PotatoSlop/Nob/SLDPRT/v3baseCollar.SLDPRT

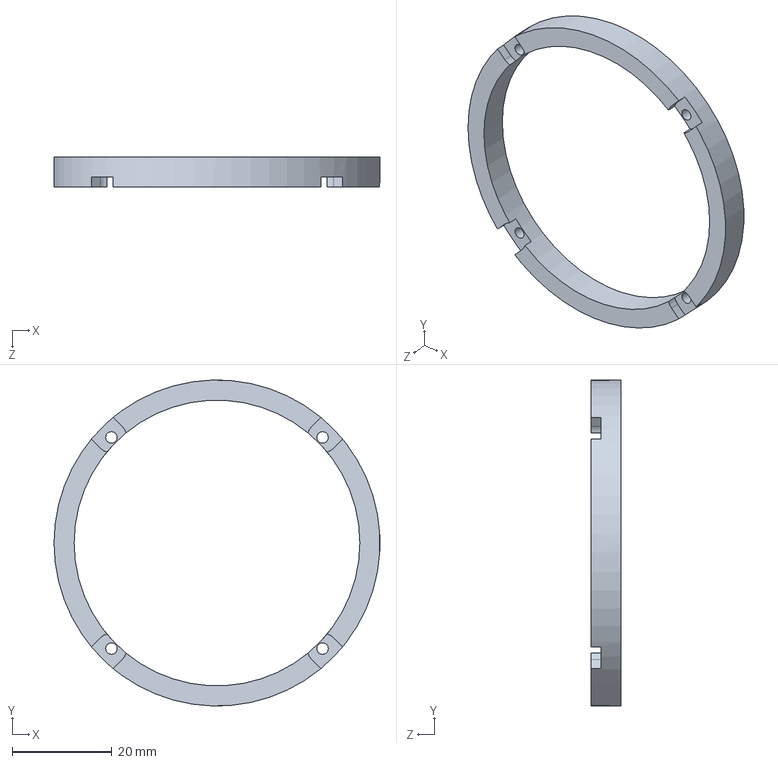
[picture p20: CAD file, 2026-09-04]
SLDPRT/v3baseCollar.SLDPRT
65.5 x 65.5 x 6.00 mm
