PotatoSlop/Nob/SLDPRT/Reference 3D Models/focus-dial-main/focus-dial-main/cad/STLs/Bezel.stl

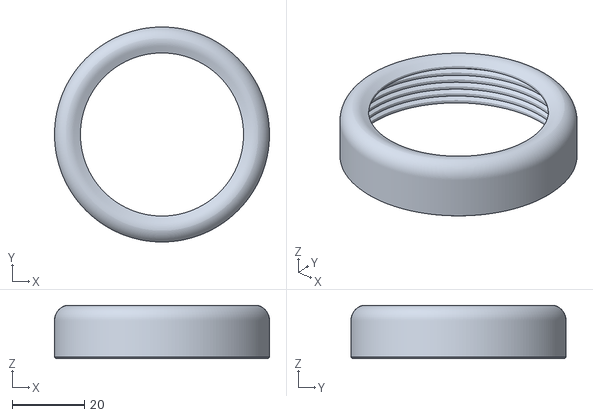
[picture p21: CAD file, 2025-09-17]
SLDPRT/Reference 3D Models/focus-dial-main/focus-dial-main/cad/STLs/Bezel.stl
59.6 x 59.6 x 14.7
