PotatoSlop/Nob/SLDPRT/shell_top_inner_2.SLDPRT

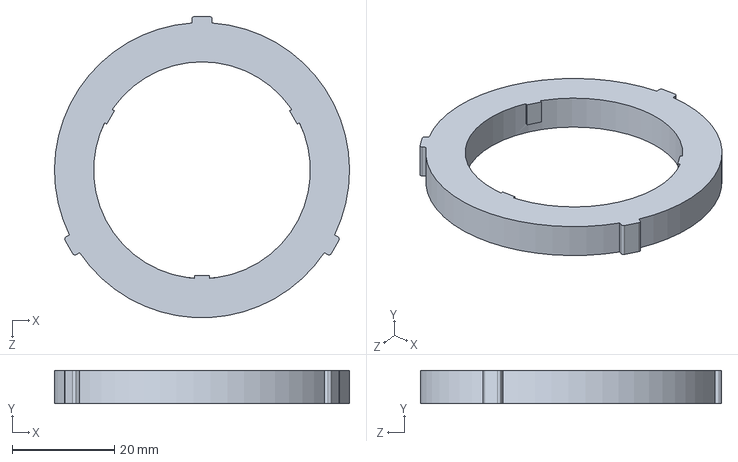
[picture p22: CAD file, 2026-09-04]
SLDPRT/shell_top_inner_2.SLDPRT
57.6 x 6.50 x 58.8 mm
