PotatoSlop/Nob/SLDPRT/Reference 3D Models/focus-dial-main/focus-dial-main/cad/STLs/Face.stl

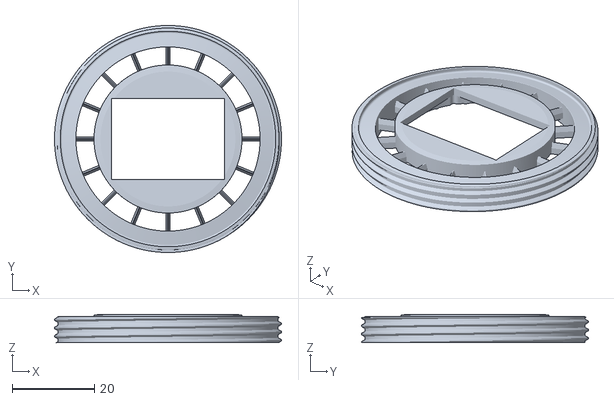
[picture p23: CAD file, 2025-09-17]
SLDPRT/Reference 3D Models/focus-dial-main/focus-dial-main/cad/STLs/Face.stl
55.2 x 55.2 x 6.90
