PotatoSlop/Nob/SLDPRT/Reference 3D Models/focus-dial-main/focus-dial-main/cad/STLs/Button Cap.stl

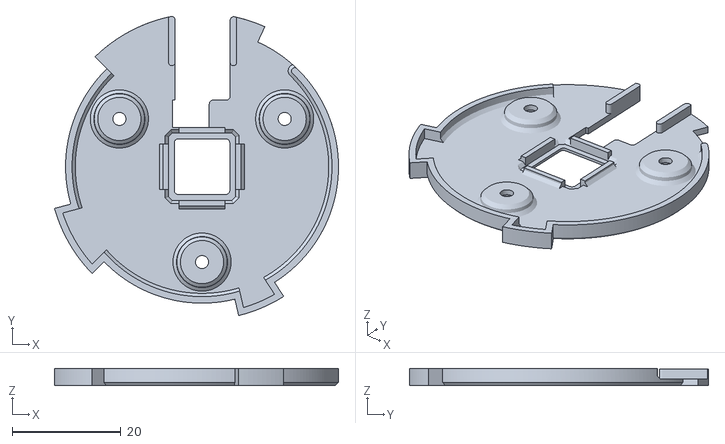
[picture p24: CAD file, 2025-09-17]
SLDPRT/Reference 3D Models/focus-dial-main/focus-dial-main/cad/STLs/Button Cap.stl
52.2 x 55.0 x 3.20
