PotatoSlop/Nob/SLDPRT/v3baseShellTopHalf.SLDPRT

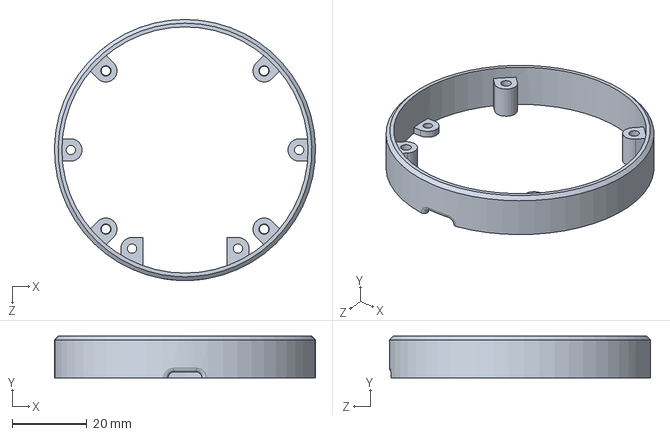
[picture p25: CAD file, 2026-09-04]
SLDPRT/v3baseShellTopHalf.SLDPRT
70.0 x 11.2 x 70.0 mm
