PotatoSlop/Nob/SLDPRT/Reference 3D Models/focus-dial-main/focus-dial-main/cad/STLs/Screen Backing.stl

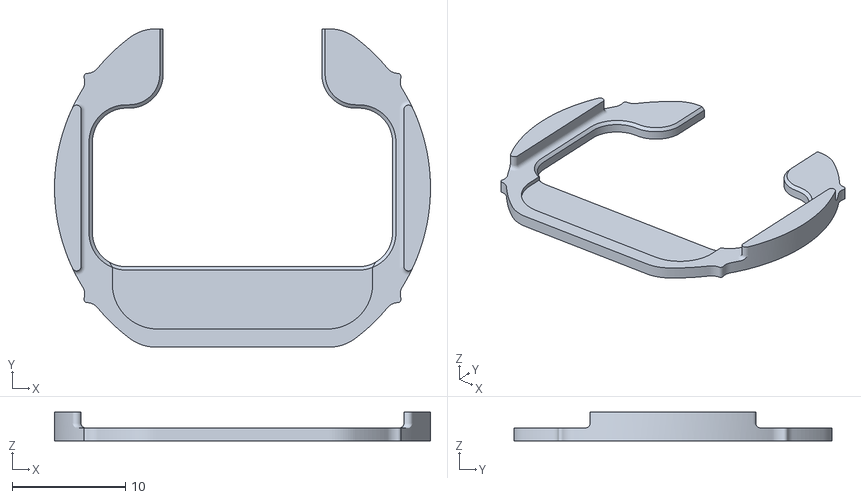
[picture p26: CAD file, 2025-09-17]
SLDPRT/Reference 3D Models/focus-dial-main/focus-dial-main/cad/STLs/Screen Backing.stl
33.2 x 28.1 x 2.55
