PotatoSlop/Nob/SLDPRT/Reference 3D Models/focus-dial-main/focus-dial-main/cad/STLs/Central Shaft.stl

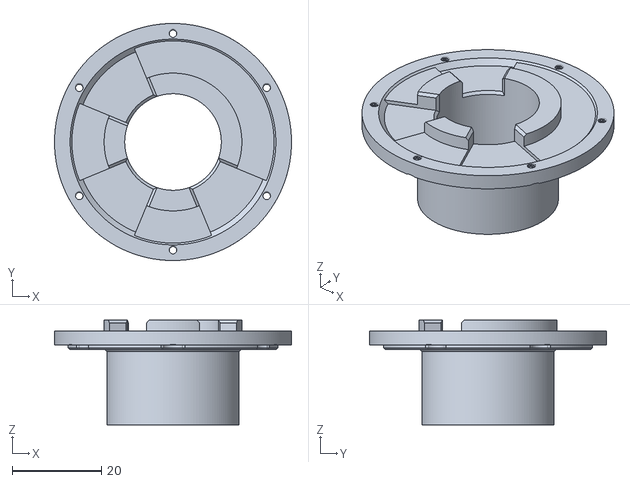
[picture p27: CAD file, 2025-09-17]
SLDPRT/Reference 3D Models/focus-dial-main/focus-dial-main/cad/STLs/Central Shaft.stl
53.0 x 53.0 x 23.4
