PotatoSlop/Nob/SLDPRT/Full.SLDASM

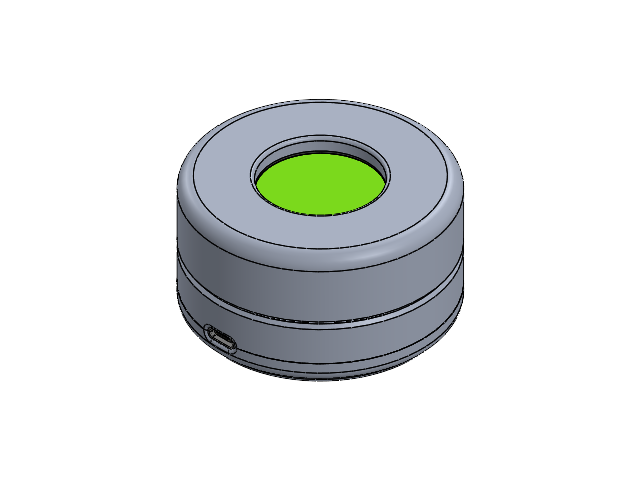
[picture p29: CAD file, 2026-09-04]
SLDPRT/Full.SLDASM
baseShellBotHalf
baseShellTopHalf
External Case.step
Steel Plate.step
Push Button.step
Component4.step x 4
EC50A0920404.step
shell_top_inner_2
inner_tube
Shell_top2_1
LCD 1.28 Inch GC9A01.stp
BOSS-EXTRUDE14_8_.step
BOSS-EXTRUDE7_4_.step
BOSS-EXTRUDE7_3_.step
BOSS-EXTRUDE14_4_.step
BOSS-EXTRUDE14_2_.step
BOSS-EXTRUDE14_11_.step
BOSS-EXTRUDE7_7_.step
BOSS-EXTRUDE14_9_.step
BOSS-EXTRUDE14_3_.step
BOSS-EXTRUDE14_7_.step
MIRROR2.step
BOSS-EXTRUDE14_5_.step
BOSS-EXTRUDE14_12_.step
BOSS-EXTRUDE7_8_.step
BOSS-EXTRUDE7_1_.step
BOSS-EXTRUDE14_10_.step
BOSS-EXTRUDE7_9_.step
BOSS-EXTRUDE14_6_.step
CHAMFER9.step
BOSS-EXTRUDE14_1_.step
BOSS-EXTRUDE7_6_.step
BOSS-EXTRUDE7_2_.step
CUT-EXTRUDE5.step
BOSS-EXTRUDE7_5_.step
U.FL Connector v1.step
Shield.step
Seeed Studio XIAO-ESP32-C6-0.step
Seeed Studio XIAO-ESP32-C6-1.step
Seeed Studio XIAO-ESP32-C6-2.step
SKTAAAE010.step x 2
KH5220-A36 (Ceramic Antenna) v2.step
pan head tapping screw_am x 6
button_cover
base_encoder_spring_var
